M1S2/PSFgen_HW/Electrical/ILI9341_with_XPT2046_Adaption.jpg

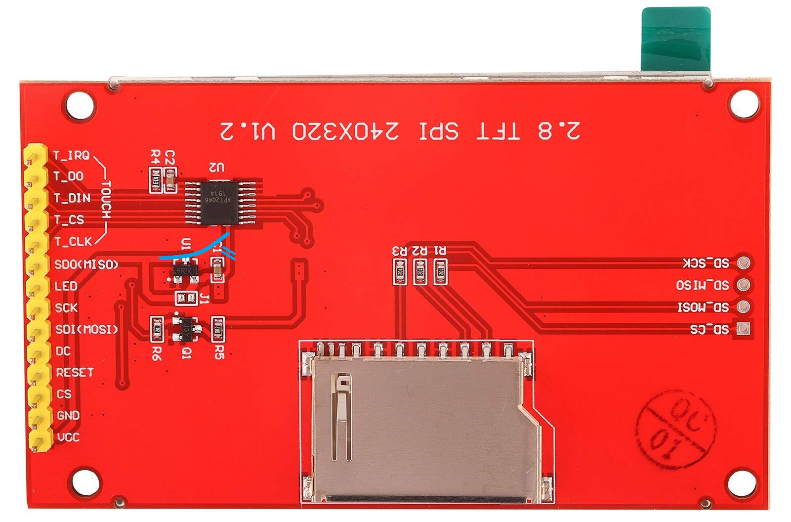
Electrical/ILI9341_with_XPT2046_Adaption.jpg
