M1S2/PSFgen_HW/Images/HW_DMMRectifier_2.jpg

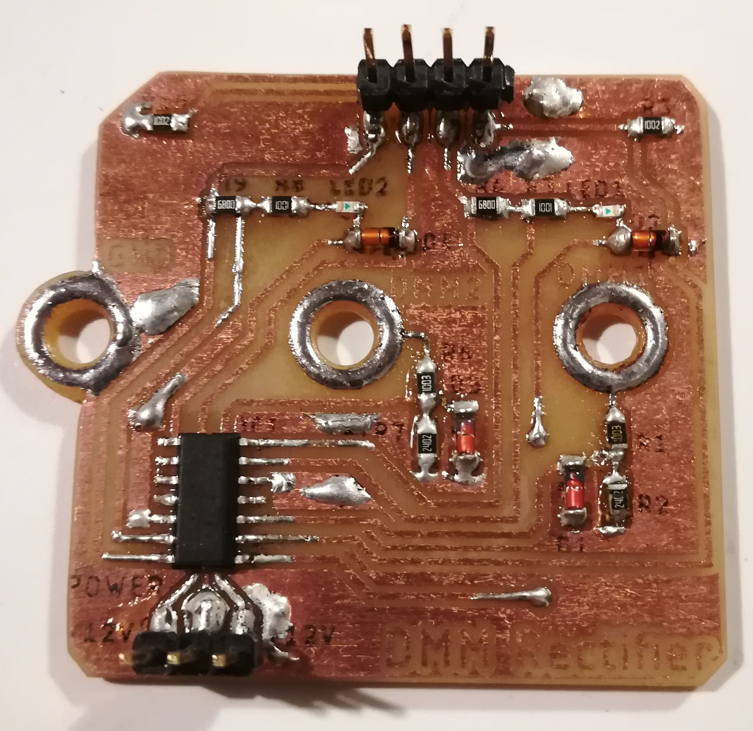
Images/HW_DMMRectifier_2.jpg
