M1S2/PSFgen_HW/Mechanical/Seitenteil_links_v56.stl

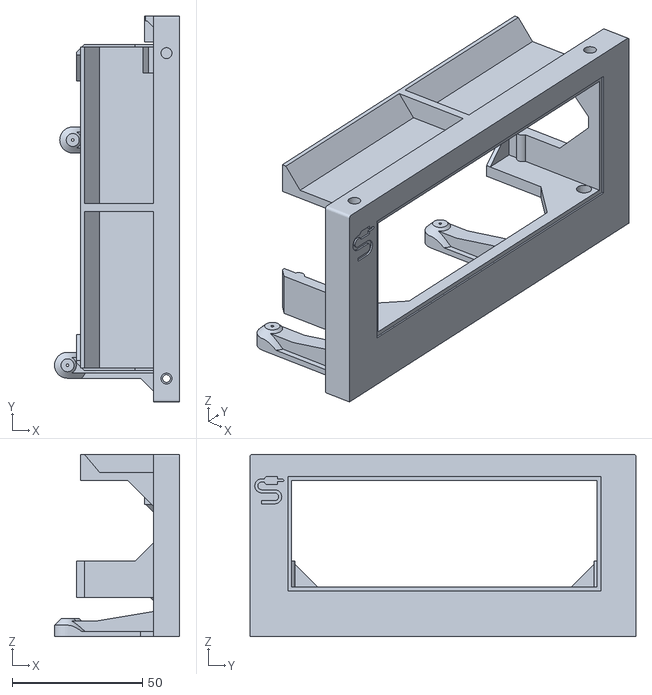
[picture p25: CAD file, 2025-01-18]
Mechanical/Seitenteil_links_v56.stl
48.0 x 148.2 x 70.0
