M1S2/PSFgen_HW/Mechanical/TFT_Holder_1_v4.stl

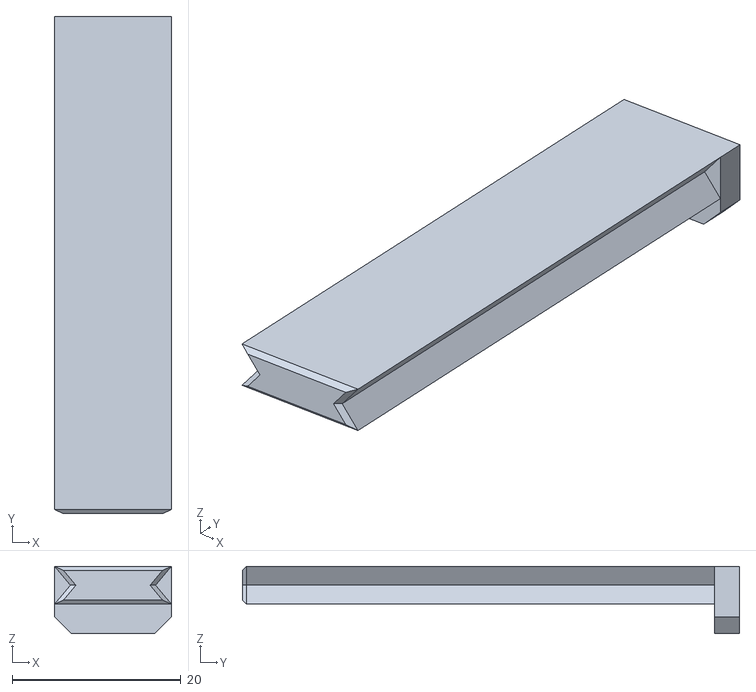
[picture p26: CAD file, 2025-01-18]
Mechanical/TFT_Holder_1_v4.stl
13.9 x 59.0 x 8.00
