M1S2/PSFgen_HW/Mechanical/Griff_v56.stl

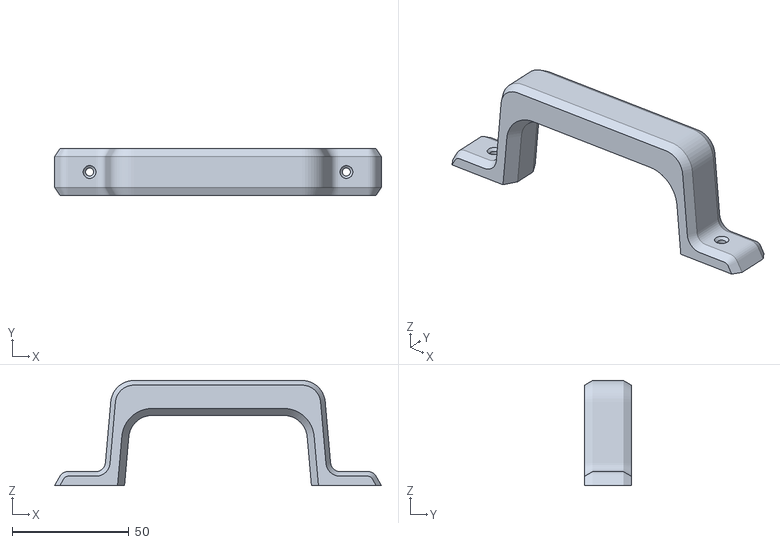
[picture p27: CAD file, 2025-01-18]
Mechanical/Griff_v56.stl
140.0 x 20.0 x 45.0
