M1S2/PSFgen_HW/Mechanical/FrontPanel_Rahmen_Schrift_v56.stl

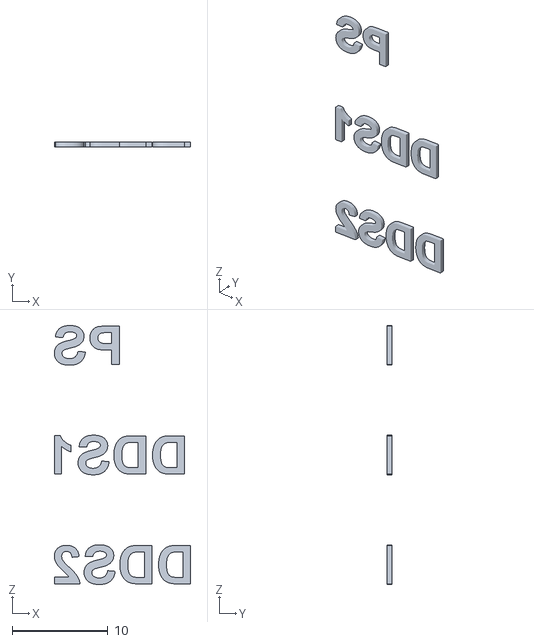
[picture p28: CAD file, 2025-01-18]
Mechanical/FrontPanel_Rahmen_Schrift_v56.stl
14.2 x 0.5 x 27.0
