M1S2/PSFgen_HW/Mechanical/Seitenteil_links_Schublade_v56.stl

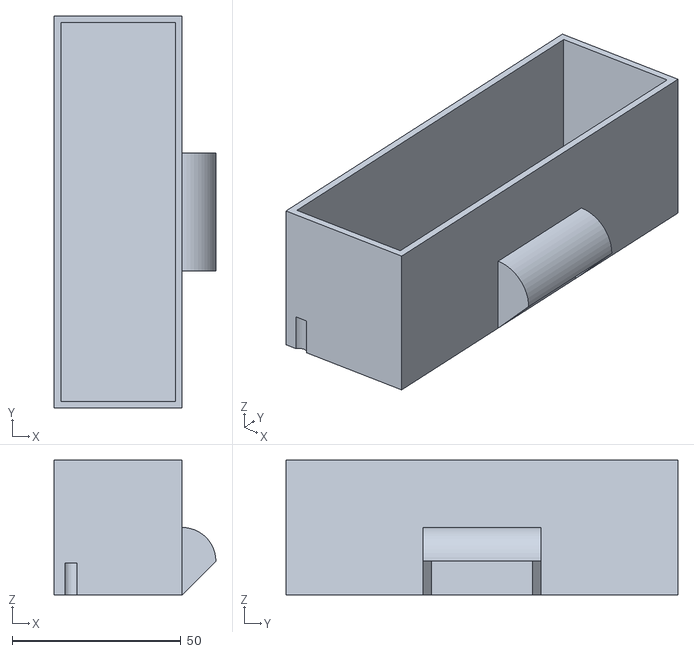
[picture p29: CAD file, 2025-01-18]
Mechanical/Seitenteil_links_Schublade_v56.stl
48.0 x 116.3 x 40.0
