M1S2/PSFgen_HW/Mechanical/Encoder_Knopf_v56.stl

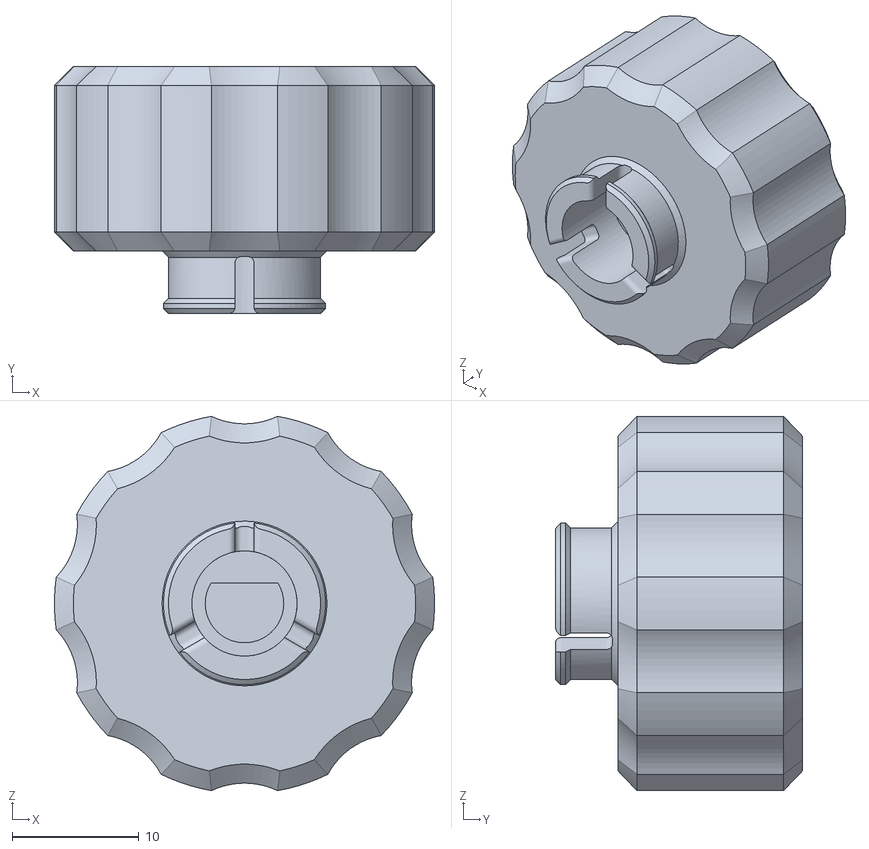
[picture p30: CAD file, 2025-01-18]
Mechanical/Encoder_Knopf_v56.stl
30.0 x 19.5 x 29.5
