M1S2/PSFgen_HW/Mechanical/FrontPanel_Rahmen_v56.stl

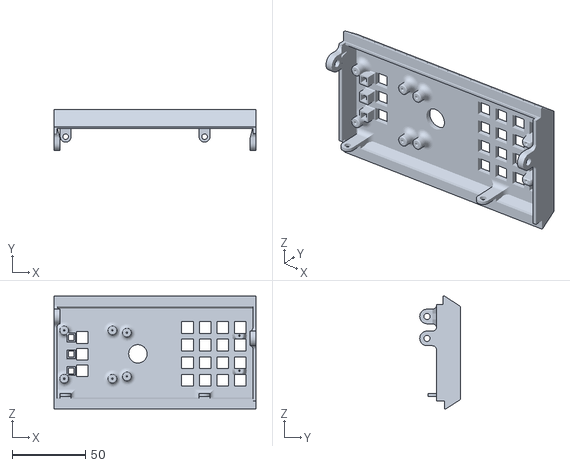
[picture p31: CAD file, 2025-01-18]
Mechanical/FrontPanel_Rahmen_v56.stl
138.2 x 27.8 x 77.3
