M1S2/PSFgen_HW/Images/HW_Assembly2.jpg

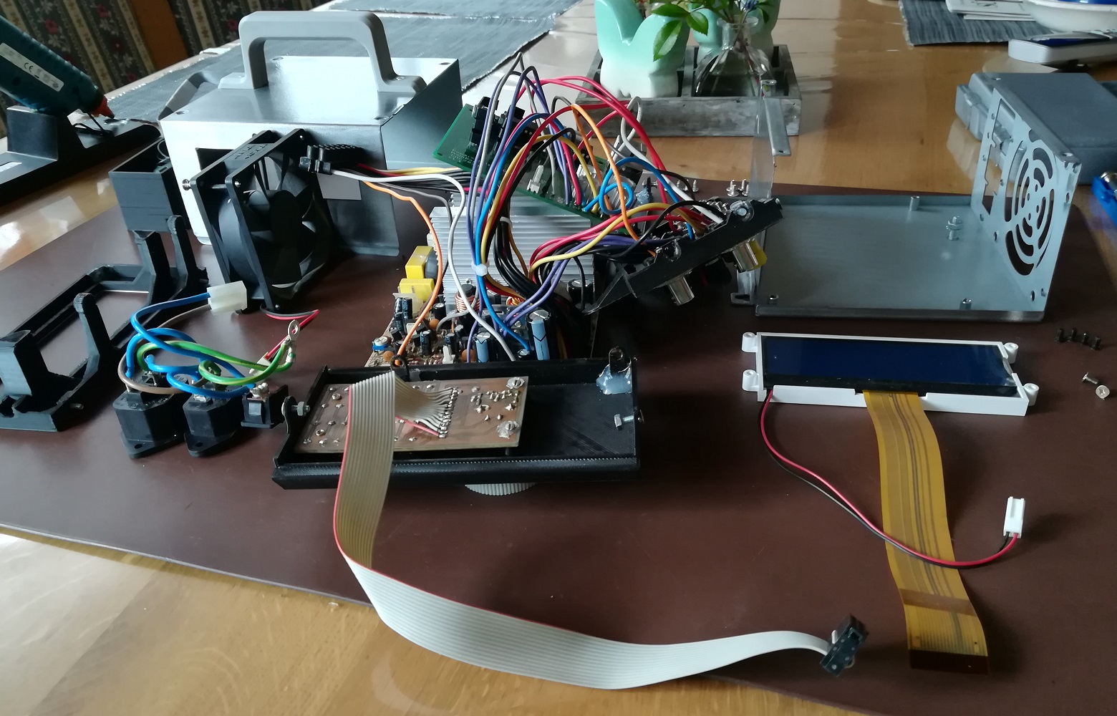
Images/HW_Assembly2.jpg
