M1S2/PSFgen_HW/Images/HW_Assembly3.jpg

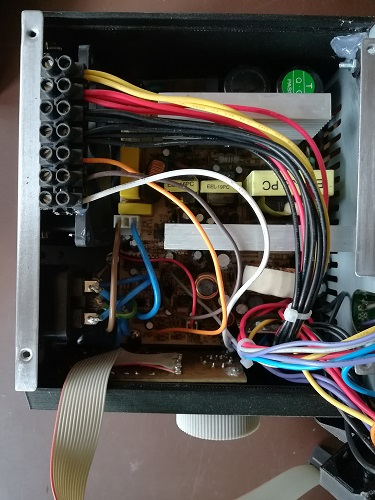
Images/HW_Assembly3.jpg
