M1S2/PSFgen_HW/Images/HW_KeyPad_Assembly_Back.jpg

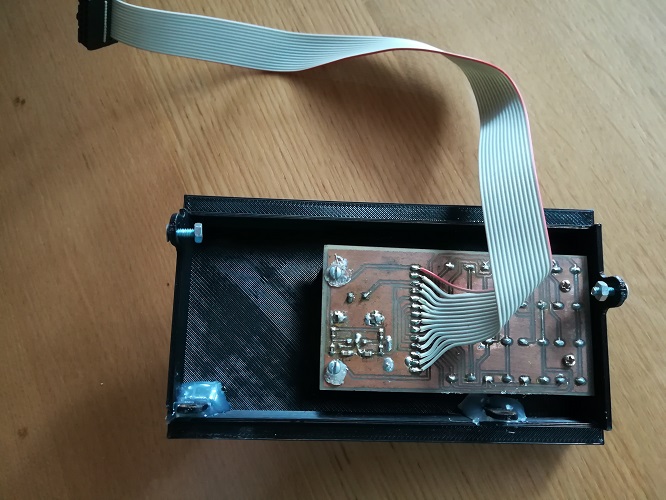
Images/HW_KeyPad_Assembly_Back.jpg
