M1S2/PSFgen_HW/Images/HW_KeyPad_Assembly_Front.jpg

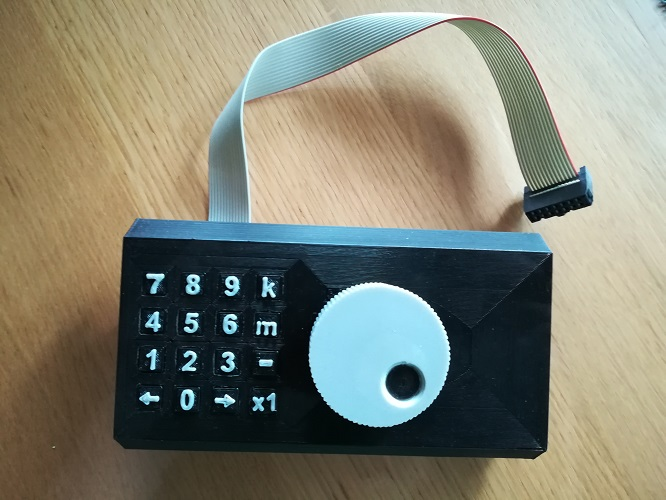
Images/HW_KeyPad_Assembly_Front.jpg
