M1S2/PSFgen_HW/Electrical/DMMRectifier/Simulation/PrecisionRectifier.asc

D1: diode
D2: LED
R1: res; 24k
R2: res; 100k
R3: res; 1000k
R4: res; 1k
R5: res; 420
R6: res; 1k
U1: UniversalOpamp2
U2: UniversalOpamp2
V1: voltage; 12
V2: voltage; 12
V3: voltage; 20
Named nets: 0, +12V, -12V, OUT, NEG?, IN
.dc V3 -20 20 1
U2 used to detect negative voltage (U1 at it's negative limit) and convert to TTL
R6 is used as resistor for the LED D2 (R4 isn't necessary anymore)
R3 isn't neede here
